KaiPereira/CYBERPAD-01/journal/IMG_1542.jpg

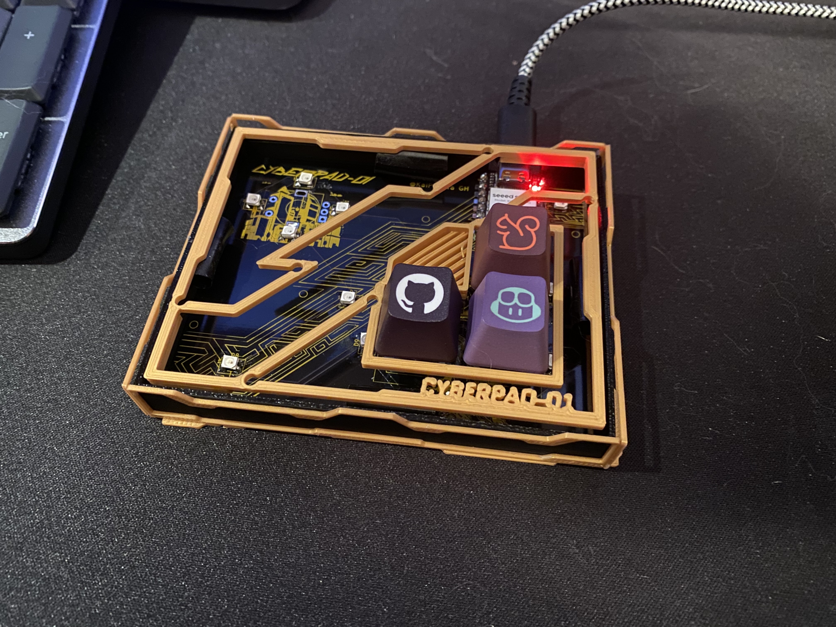
journal/IMG_1542.jpg
