KaiPereira/CYBERPAD-01/journal/Pasted image 20250702021444.png

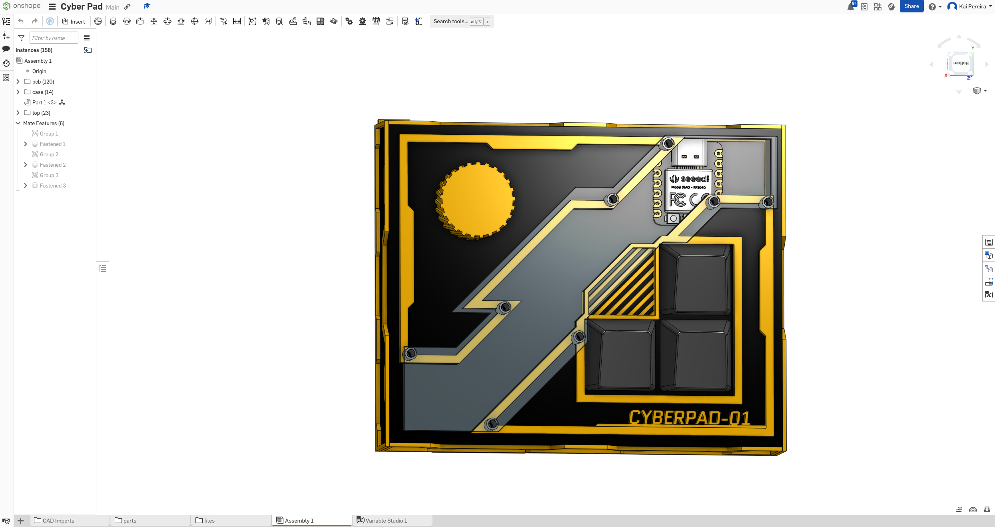
journal/Pasted image 20250702021444.png
