KaiPereira/CYBERPAD-01/journal/Pasted image 20250705163430.png

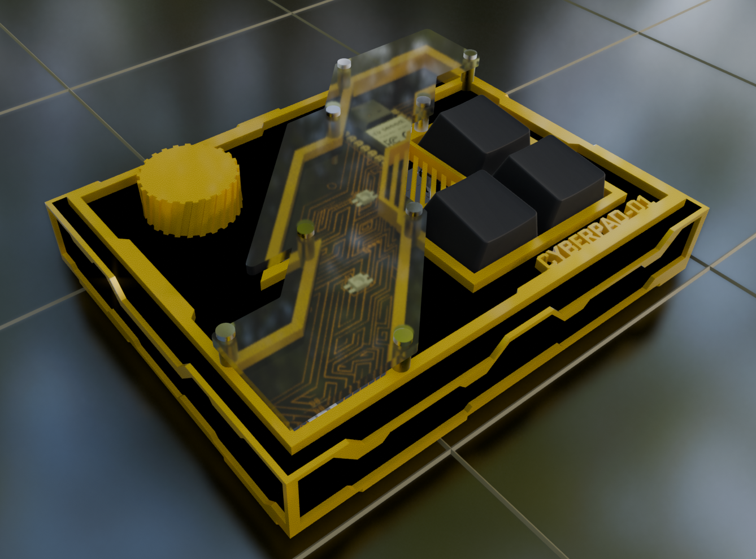
journal/Pasted image 20250705163430.png
