KaiPereira/CYBERPAD-01/journal/Pasted image 20250705183413.png

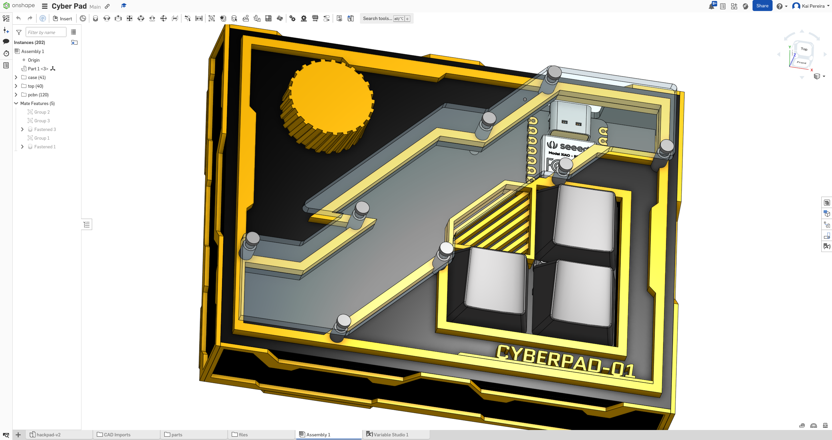
journal/Pasted image 20250705183413.png
