KaiPereira/CYBERPAD-01/journal/Pasted image 20250705183446.png

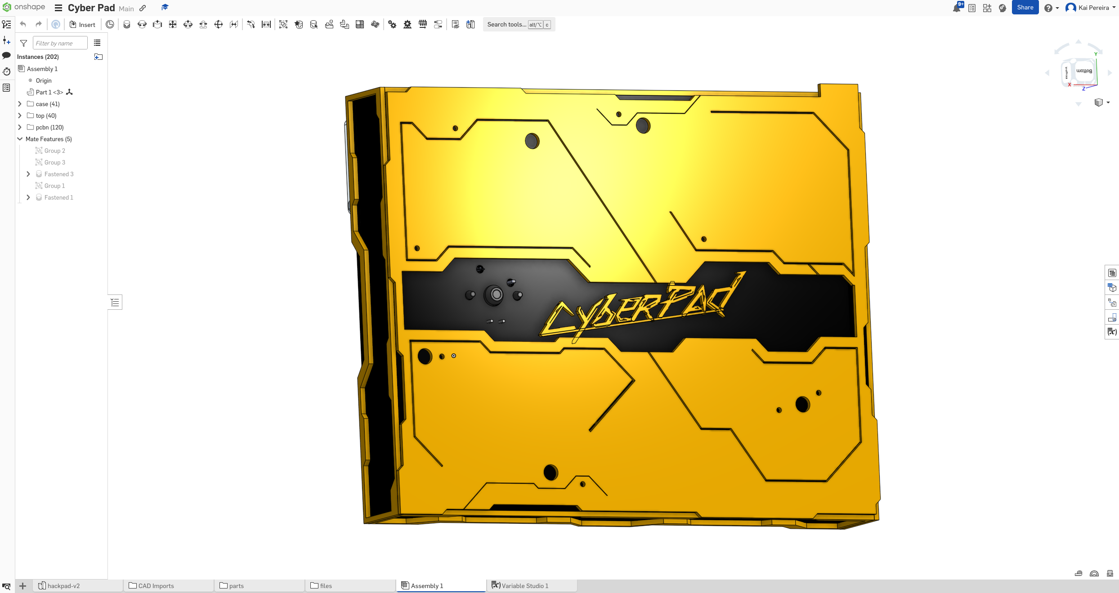
journal/Pasted image 20250705183446.png
